bootsector/usb-retropad-adapter/src/genesis.cpp

/*
* USB RetroPad Adapter - PC/PS3 USB adapter for retro-controllers!
* Copyright (c) 2012 Bruno Freitas - bruno@brunofreitas.com
*
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
* You should have received a copy of the GNU General Public License
* along with this program.  If not, see <http://www.gnu.org/licenses/>.
 */

#include <WProgram.h>
#include "genesis.h"
#include "digitalWriteFast.h"

#define DB9P1 5
#define DB9P2 6
#define DB9P3 7
#define DB9P4 8
#define DB9P6 9
#define DB9P7 10
#define DB9P9 11

#define DELAY 14

void genesis_init() {
	pinModeFast(DB9P1, INPUT);
	pinModeFast(DB9P2, INPUT);
	pinModeFast(DB9P3, INPUT);
	pinModeFast(DB9P4, INPUT);
	pinModeFast(DB9P6, INPUT);
	pinModeFast(DB9P7, OUTPUT);
	pinModeFast(DB9P9, INPUT);

	digitalWriteFast(DB9P1, HIGH);
	digitalWriteFast(DB9P2, HIGH);
	digitalWriteFast(DB9P3, HIGH);
	digitalWriteFast(DB9P4, HIGH);
	digitalWriteFast(DB9P6, HIGH);
	digitalWriteFast(DB9P7, HIGH);
	digitalWriteFast(DB9P9, HIGH);
}

int genesis_read() {
	int retval;

	int extrabuttons = 0;
	int normalbuttons = 0;

	// Get D-PAD, B, C buttons state
	digitalWriteFast(DB9P7, HIGH);
	delayMicroseconds(DELAY);

	normalbuttons |= (!digitalReadFast(DB9P1) << 0);
	normalbuttons |= (!digitalReadFast(DB9P2) << 1);
	normalbuttons |= (!digitalReadFast(DB9P3) << 2);
	normalbuttons |= (!digitalReadFast(DB9P4) << 3);
	normalbuttons |= (!digitalReadFast(DB9P6) << 4);
	normalbuttons |= (!digitalReadFast(DB9P9) << 5);

	digitalWriteFast(DB9P7, LOW);
	delayMicroseconds(DELAY);

	// Is using a SEGA Genesis controller, LEFT and RIGHT will be ACTIVE here
	if(!(!digitalReadFast(DB9P3) && !digitalReadFast(DB9P4))) {
		retval = normalbuttons | (extrabuttons << 8);
		return retval;
	}

	// Get A and START buttons state
	normalbuttons |= (!digitalReadFast(DB9P6) << 6);
	normalbuttons |= (!digitalReadFast(DB9P9) << 7);

	digitalWriteFast(DB9P7, HIGH);
	delayMicroseconds(DELAY);
	digitalWriteFast(DB9P7, LOW);
	delayMicroseconds(DELAY);

	// Up, Down, Left and Right are low if 6-button controller
	if(!digitalReadFast(DB9P1) && !digitalReadFast(DB9P2) && !digitalReadFast(DB9P3) && !digitalReadFast(DB9P4)) {
		digitalWriteFast(DB9P7, HIGH);
		delayMicroseconds(DELAY);

		extrabuttons |= (!digitalReadFast(DB9P1) << 0);
		extrabuttons |= (!digitalReadFast(DB9P2) << 1);
		extrabuttons |= (!digitalReadFast(DB9P3) << 2);
		extrabuttons |= (!digitalReadFast(DB9P4) << 3);

		digitalWriteFast(DB9P7, LOW);
		delayMicroseconds(DELAY);
		digitalWriteFast(DB9P7, HIGH);
		delayMicroseconds(DELAY);
		digitalWriteFast(DB9P7, LOW);

		// Delay needed for settling joystick down
		delayMicroseconds(2000);
	}

	retval = normalbuttons | (extrabuttons << 8);

	return retval;
}
