bootsector/usb-retropad-adapter/src/saturn.cpp

/*
* USB RetroPad Adapter - PC/PS3 USB adapter for retro-controllers!
* Copyright (c) 2012 Bruno Freitas - bruno@brunofreitas.com
*
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
* You should have received a copy of the GNU General Public License
* along with this program.  If not, see <http://www.gnu.org/licenses/>.
 */

#include <WProgram.h>
#include "saturn.h"
#include "digitalWriteFast.h"

#define D1 5
#define D0 6
#define S0 7
#define S1 9
#define D3 10
#define D2 11

#define DELAY 4

void saturn_init() {
	pinModeFast(D1, INPUT);
	pinModeFast(D0, INPUT);
	pinModeFast(D3, INPUT);
	pinModeFast(D2, INPUT);
	pinModeFast(S0, OUTPUT);
	pinModeFast(S1, OUTPUT);

	digitalWriteFast(D1, HIGH);
	digitalWriteFast(D0, HIGH);
	digitalWriteFast(D3, HIGH);
	digitalWriteFast(D2, HIGH);

	digitalWriteFast(S0, HIGH);
	digitalWriteFast(S1, HIGH);
}

int saturn_read() {
	int retval = 0;

	/*
	* S0	S1		D0	d1	d2	d3
	* Off 	Off 	Z 	Y 	X 	R
	* On 	Off 	B 	C 	A 	St
	* Off 	On 		Up 	Dn 	Lt 	Rt
	* On 	On 		- 	- 	- 	L
	*/

	// Reading L
	digitalWriteFast(S0, HIGH);
	digitalWriteFast(S1, HIGH);
	delayMicroseconds(DELAY);

	retval |= (!digitalReadFast(D3) << 12); // L

	// Reading Z, Y, X and R
	digitalWriteFast(S0, LOW);
	digitalWriteFast(S1, LOW);
	delayMicroseconds(DELAY);

	retval |= (!digitalReadFast(D0) << 0); // Z
	retval |= (!digitalReadFast(D1) << 1); // Y
	retval |= (!digitalReadFast(D2) << 2); // X
	retval |= (!digitalReadFast(D3) << 3); // R

	// Reading B, C, A and Start
	digitalWriteFast(S0, HIGH);
	digitalWriteFast(S1, LOW);
	delayMicroseconds(DELAY);

	retval |= (!digitalReadFast(D0) << 4); // B
	retval |= (!digitalReadFast(D1) << 5); // C
	retval |= (!digitalReadFast(D2) << 6); // A
	retval |= (!digitalReadFast(D3) << 7); // Start

	// Reading Up, Down, Left, Right
	digitalWriteFast(S0, LOW);
	digitalWriteFast(S1, HIGH);
	delayMicroseconds(DELAY);

	retval |= (!digitalReadFast(D0) << 8); // Up
	retval |= (!digitalReadFast(D1) << 9); // Down
	retval |= (!digitalReadFast(D2) << 10); // Left
	retval |= (!digitalReadFast(D3) << 11); // Right

	return retval;
}
