bootsector/usb-retropad-adapter/src/USBVirtuaStick.h

/*
* USB RetroPad Adapter - PC/PS3 USB adapter for retro-controllers!
* Copyright (c) 2012 Bruno Freitas - bruno@brunofreitas.com
*
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
* You should have received a copy of the GNU General Public License
* along with this program.  If not, see <http://www.gnu.org/licenses/>.
 */

#ifndef USBVIRTUASTICK_H_
#define USBVIRTUASTICK_H_

#include <avr/io.h>
#include <avr/wdt.h>
#include <avr/interrupt.h>  /* for sei() */
#include <util/delay.h>     /* for _delay_ms() */
#include <string.h>			/* for memset() */

#include <avr/pgmspace.h>   /* required by usbdrv.h */

extern "C" {				/* without extern "C", this won't link as a .cpp file */
#include "usbdrv.h"
}

typedef struct {
	// digital buttons, 0 = off, 1 = on

	uint8_t square_btn : 1;
	uint8_t cross_btn : 1;
	uint8_t circle_btn : 1;
	uint8_t triangle_btn : 1;

	uint8_t l1_btn : 1;
	uint8_t r1_btn : 1;
	uint8_t l2_btn : 1;
	uint8_t r2_btn : 1;

	uint8_t select_btn : 1;
	uint8_t start_btn : 1;
	uint8_t l3_btn : 1;
	uint8_t r3_btn : 1;
	uint8_t ps_btn : 1;
	uint8_t : 3;

	// digital direction, use the dir_* constants(enum)
	// 8 = center, 0 = up, 1 = up/right, 2 = right, 3 = right/down
	// 4 = down, 5 = down/left, 6 = left, 7 = left/up

	uint8_t direction;

	// left and right analog sticks, 0x00 left/up, 0x80 middle, 0xff right/down

	uint8_t l_x_axis;
	uint8_t l_y_axis;
	uint8_t r_x_axis;
	uint8_t r_y_axis;
	uint8_t slider;

	uint8_t unknown[4];

	// button axis, 0x00 = unpressed, 0xff = fully pressed

	uint8_t triangle_axis;
	uint8_t circle_axis;
	uint8_t cross_axis;
	uint8_t square_axis;

	uint8_t l1_axis;
	uint8_t r1_axis;
	uint8_t l2_axis;
	uint8_t r2_axis;
} gamepad_state_t;

void vs_reset_pad_status();
void vs_init(bool watchdog);
void vs_reset_watchdog();
void vs_send_pad_state();

extern gamepad_state_t gamepad_state;

#endif /* USBVIRTUASTICK_H_ */
